Silcantar/androphage/assets/renders/closed_eye.png

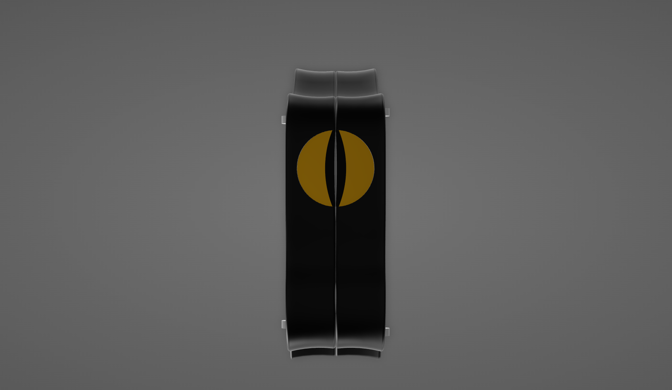
assets/renders/closed_eye.png
