Silcantar/androphage/assets/renders/quarter.png

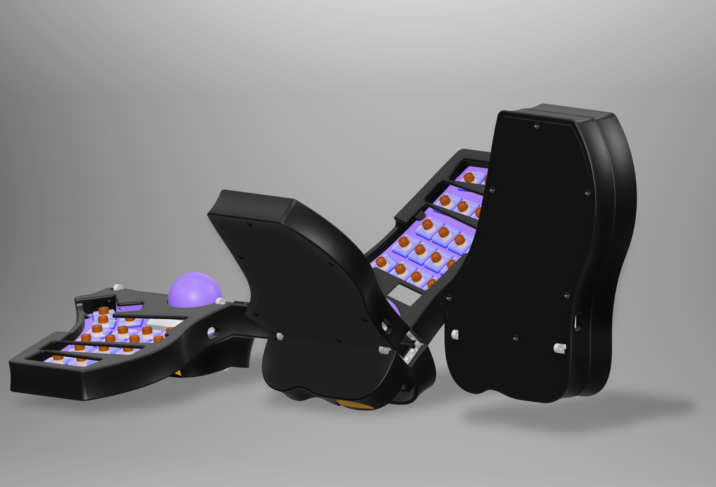
assets/renders/quarter.png
